MechRedPanda/red-panda-stm/Code/teensy/src/logTable.hpp

/**************************************************************************/
/*

Daniel Berard, daniel.berard@mail.mcgill.ca
Last updated Oct 14, 2015
http://dberard.com/home-built-stm/


Table generated using the following MATLAB code:

    x=0:32768;
    lt = round(log(x+1)*(2^19-1)/log(2^15+1))';
    fid = fopen('lt.txt', 'a');
    fprintf(fid, [repmat('%d, ', 1, size(lt, 2) - 1), '%d,\r\n'], lt.');
    fclose(fid);


logTable takes an input from 0 - 32768 (the absolute value of the input
from the 16-bit ADC) and outputs a value from 0 - 524287.

*/
/**************************************************************************/

const int logTable[32769] = {
    34952,
    34952,
    55398,
    69905,
    81157,
    90351,
    98124,
    104857,
    110796,
    116109,
    120915,
    125303,
    129339,
    133076,
    136555,
    139809,
    142866,
    145749,
    148475,
    151062,
    153522,
    155868,
    158109,
    160255,
    162314,
    164291,
    166195,
    168028,
    169798,
    171507,
    173161,
    174762,
    176313,
    177819,
    179281,
    180701,
    182083,
    183427,
    184737,
    186014,
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
